WarewolfCZ/Winner_RGB_M3A/Photo/20191223_013433.jpg

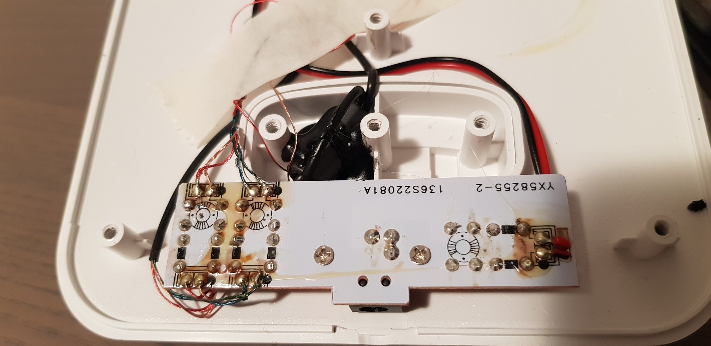
Photo/20191223_013433.jpg
