WarewolfCZ/Winner_RGB_M3A/Photo/20191223_014823.jpg

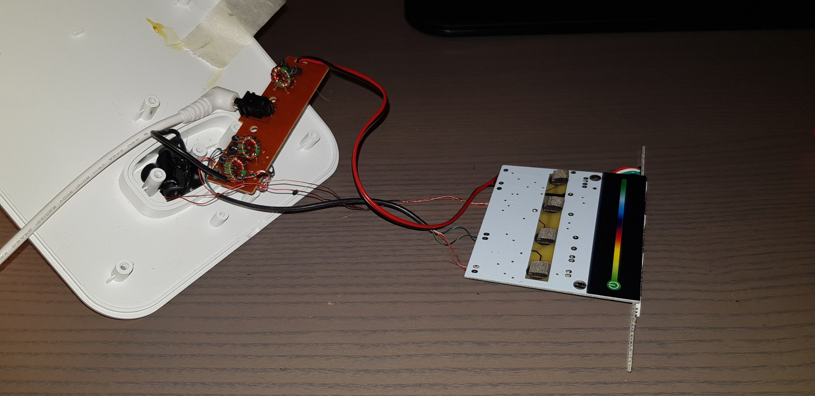
Photo/20191223_014823.jpg
