WarewolfCZ/Winner_RGB_M3A/Photo/20191223_164008.jpg

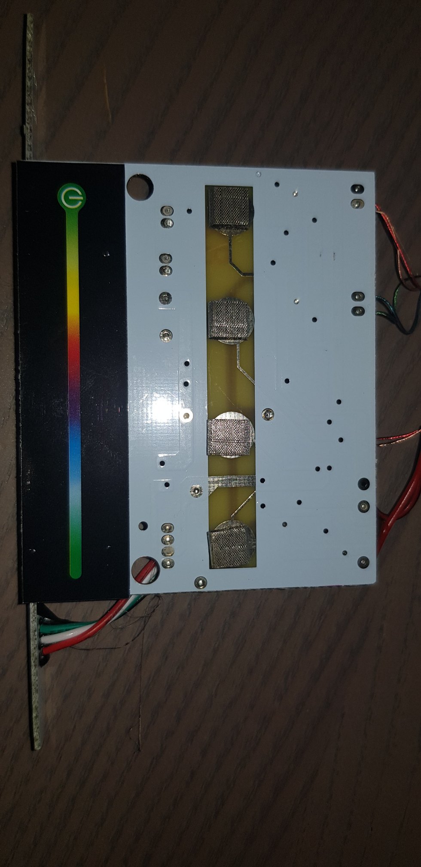
Photo/20191223_164008.jpg
