WarewolfCZ/Winner_RGB_M3A/Photo/20191223_172415.jpg

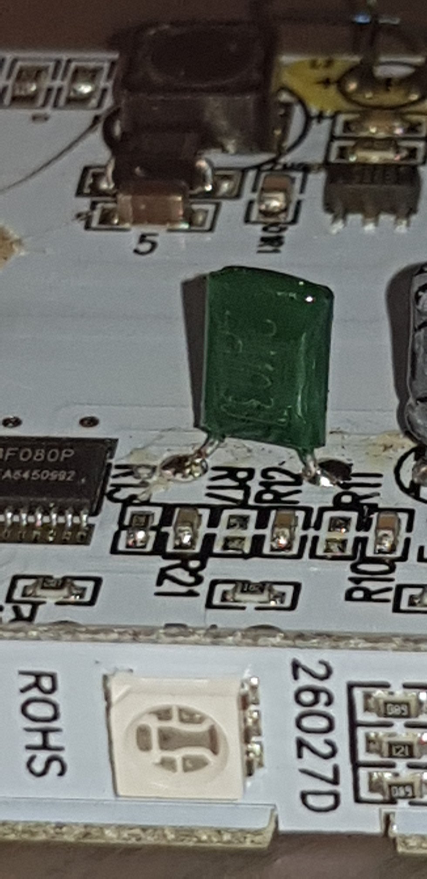
Photo/20191223_172415.jpg
