WarewolfCZ/Winner_RGB_M3A/Photo/20191223_203338.jpg

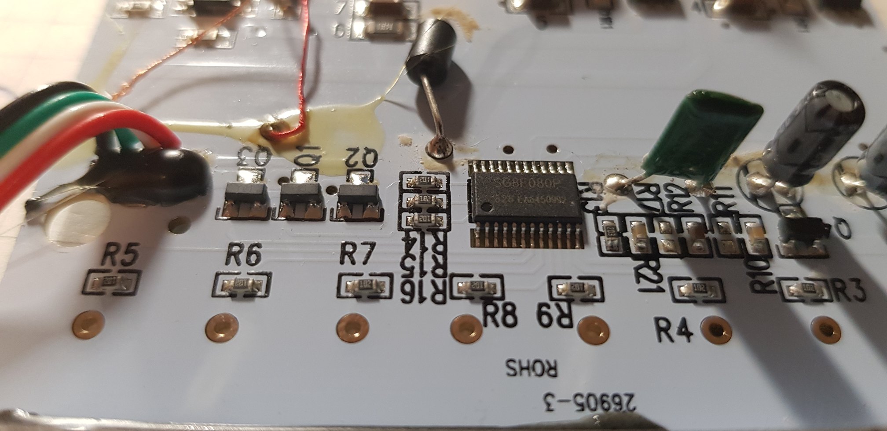
Photo/20191223_203338.jpg
