WarewolfCZ/Winner_RGB_M3A/Photo/20191223_234438.jpg

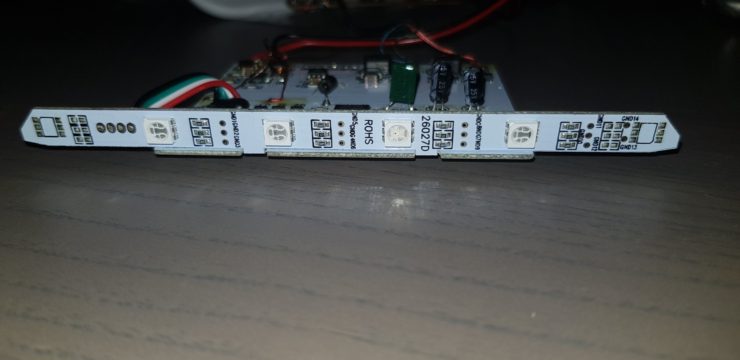
Photo/20191223_234438.jpg
